erichVK5/erichVK5-air-quality-monitor-v2/images/01-optional-header.JPG

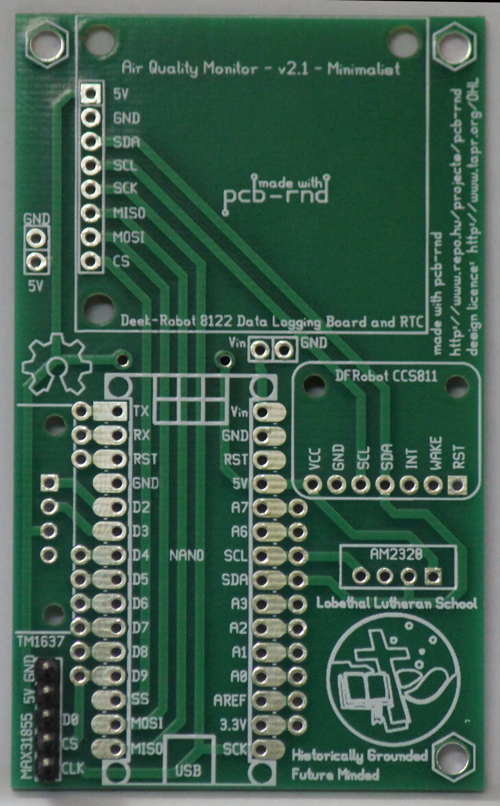
images/01-optional-header.JPG
