erichVK5/erichVK5-air-quality-monitor-v2/images/02-add-arduino-nano.JPG

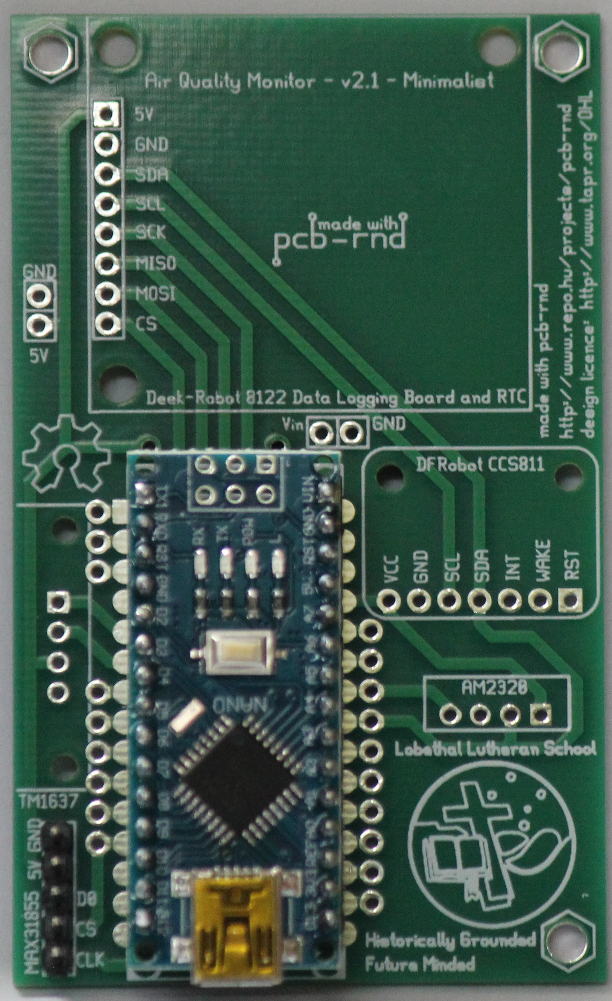
images/02-add-arduino-nano.JPG
