erichVK5/erichVK5-air-quality-monitor-v2/images/05-add-CO2-VOC-board.JPG

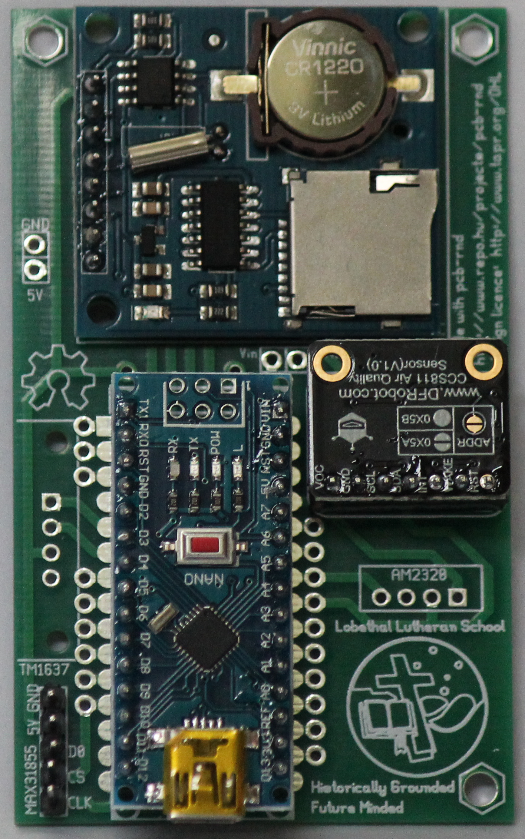
images/05-add-CO2-VOC-board.JPG
